hxcl/Protable-climate-monitor/Fianl/tem_hum/tem_hum.ino

#include <Wire.h>
void  setup()
{ 
  Serial.begin(9600);   
  Wire.begin();
                               
}
void  loop()
{
  double X,Y;
  tem_hum(X,Y);   //X是温度，Y是湿度
  delay(970);
  Serial.println();
  Serial.println();
}
void tem_hum(double &X,double &Y)
{
  pinMode(13,OUTPUT);
  const  int  ADDR =0x40;
  int  X0,X1,Y0,Y1,Y2,Y3;
  double  X_out,Y_out1,Y_out2;  
  Wire.beginTransmission(ADDR);
  Wire.endTransmission();
  Wire.beginTransmission(ADDR);
  Wire.write(0xE3);
  Wire.endTransmission();

  digitalWrite(13,HIGH);  
  Wire.requestFrom(ADDR,2);
 
  if (Wire.available()<=2);
  {
    X0 = Wire.read();
    X1 = Wire.read();
    X0 = X0<<8;
    X_out = X0+X1;
  }
  X=(175.72*X_out)/65536;                        
  X=X-46.85;
 
  Wire.beginTransmission(ADDR);                     
  Wire.write(0xE5);
  Wire.endTransmission(); 

  Wire.requestFrom(ADDR,2);
  if (Wire.available()<=2);
  {
    Y0 = Wire.read();
    Y2=Y0/100; 
    Y0=Y0%100;
    Y1 = Wire.read();
    Y_out1 = Y2*25600;
    Y_out2 = Y0*256+Y1;
  }

  Y_out1 = (125*Y_out1)/65536;                     
  Y_out2 = (125*Y_out2)/65536;
  Y = Y_out1+Y_out2;
  Y=Y-6;
  digitalWrite(13,LOW);                           
}
